Kampi/Watch-DK-HW/production/watch-dk-CHECKED/Images/ZSWatch-Watch-DevKit-angled_top.png

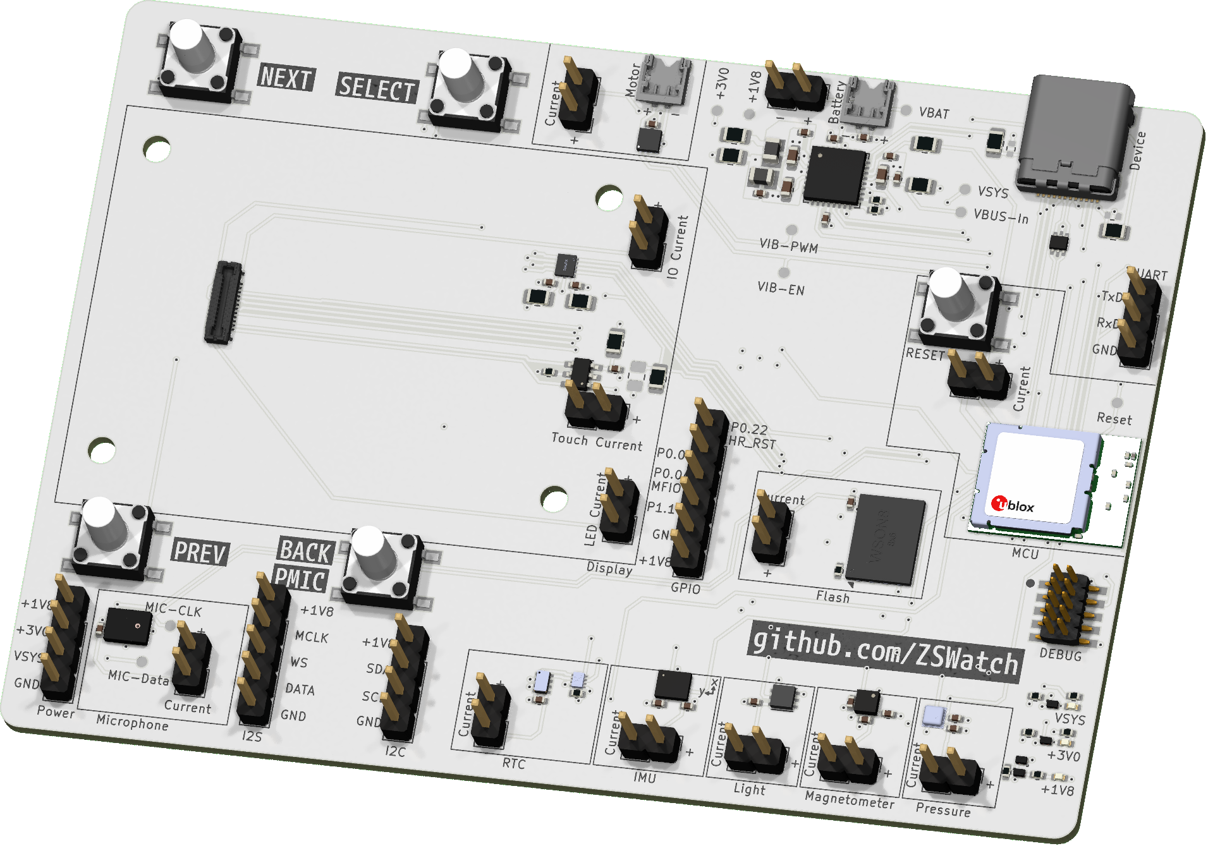
production/watch-dk-CHECKED/Images/ZSWatch-Watch-DevKit-angled_top.png
