Kampi/Watch-DK-HW/production/watch-dk-CHECKED/Images/ZSWatch-Watch-DevKit-bottom.png

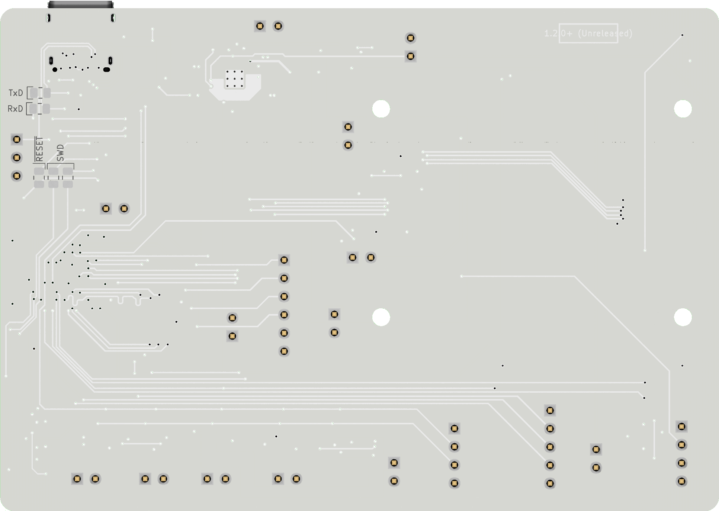
production/watch-dk-CHECKED/Images/ZSWatch-Watch-DevKit-bottom.png
