Kampi/Watch-DK-HW/production/watch-dk-RELEASED/HTML/images/cat_pdf_drill_map_ZSWatch-Watch-DevKit-NPTH_drill_map.png

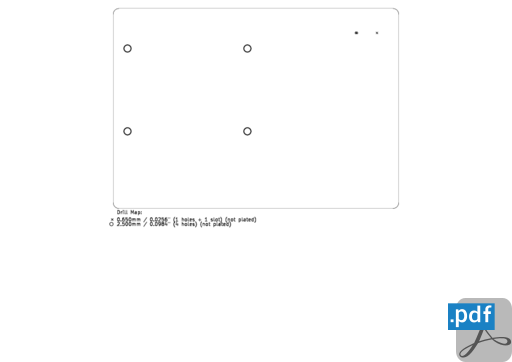
production/watch-dk-RELEASED/HTML/images/cat_pdf_drill_map_ZSWatch-Watch-DevKit-NPTH_drill_map.png
