Kampi/Watch-DK-HW/production/watch-dk-RELEASED/HTML/images/cat_png_3d_viewer_angled_bottom_ZSWatch-Watch-DevKit-angled_bottom.png

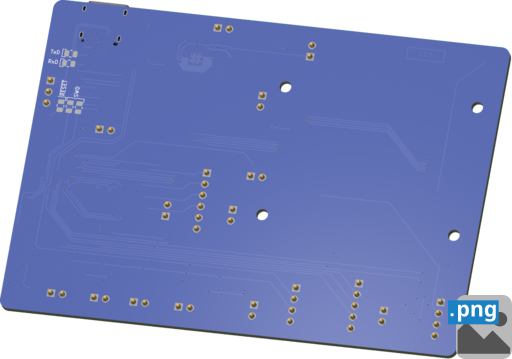
production/watch-dk-RELEASED/HTML/images/cat_png_3d_viewer_angled_bottom_ZSWatch-Watch-DevKit-angled_bottom.png
