Kampi/Watch-DK-HW/production/watch-dk-RELEASED/HTML/images/cat_png_3d_viewer_angled_top_ZSWatch-Watch-DevKit-angled_top.png

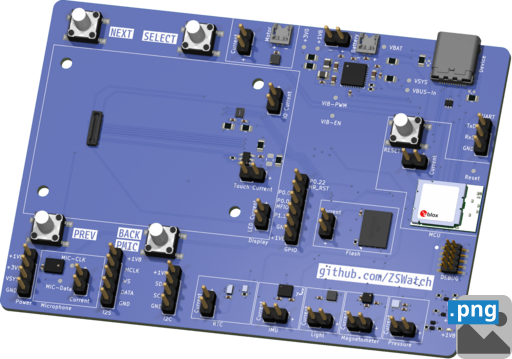
production/watch-dk-RELEASED/HTML/images/cat_png_3d_viewer_angled_top_ZSWatch-Watch-DevKit-angled_top.png
