Kampi/Watch-DK-HW/production/watch-dk-RELEASED/HTML/images/cat_pdf_assembly_ZSWatch-Watch-DevKit-assembly.png

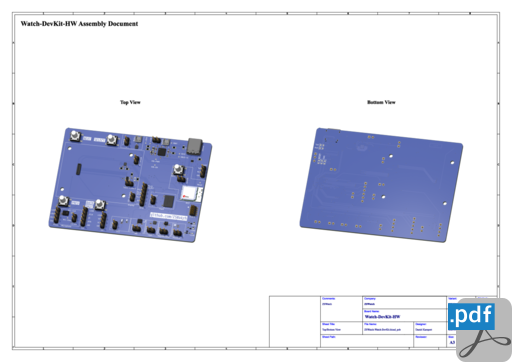
production/watch-dk-RELEASED/HTML/images/cat_pdf_assembly_ZSWatch-Watch-DevKit-assembly.png
