Kampi/Watch-DK-HW/production/watch-dk-RELEASED/HTML/images/cat_pdf_fabrication_ZSWatch-Watch-DevKit-fabrication.png

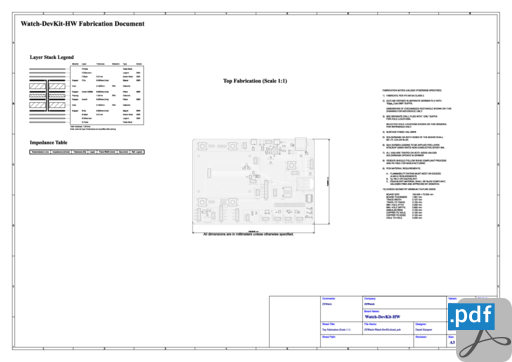
production/watch-dk-RELEASED/HTML/images/cat_pdf_fabrication_ZSWatch-Watch-DevKit-fabrication.png
